SolderedElectronics/Soldered-Air-Quality-Device/Images/3dCase1.jpg

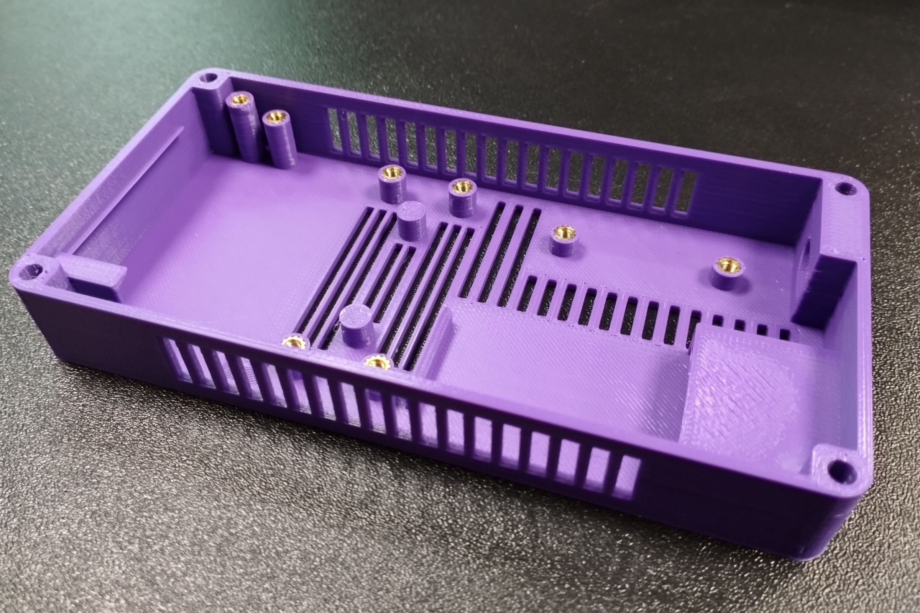
Images/3dCase1.jpg
