SolderedElectronics/Soldered-Air-Quality-Device/Images/3dCase.jpg

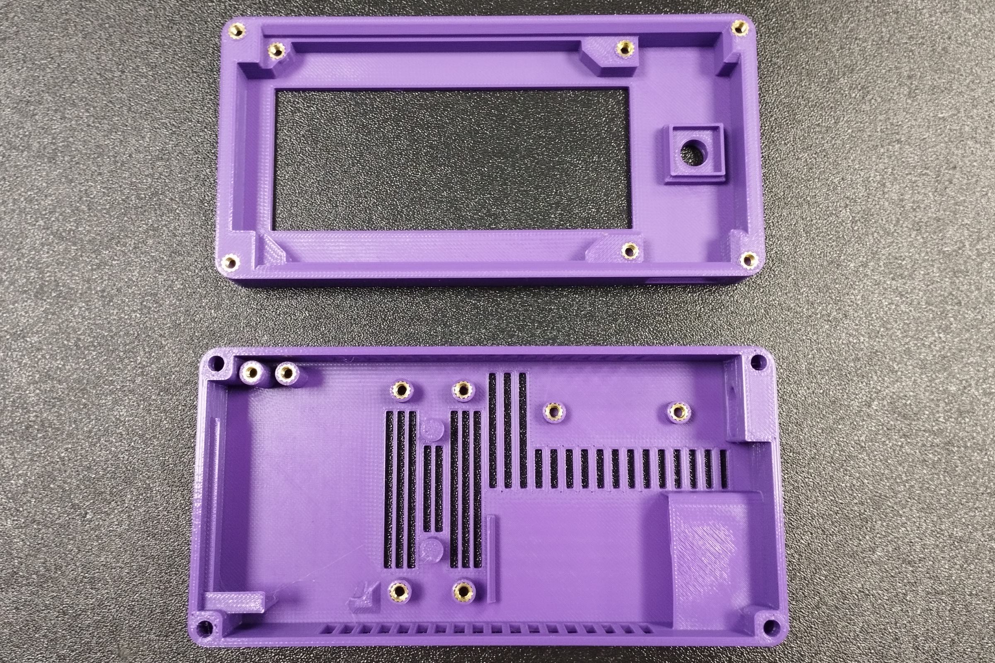
Images/3dCase.jpg
