SolderedElectronics/Soldered-Air-Quality-Device/Images/DeviceFromAbove.jpg

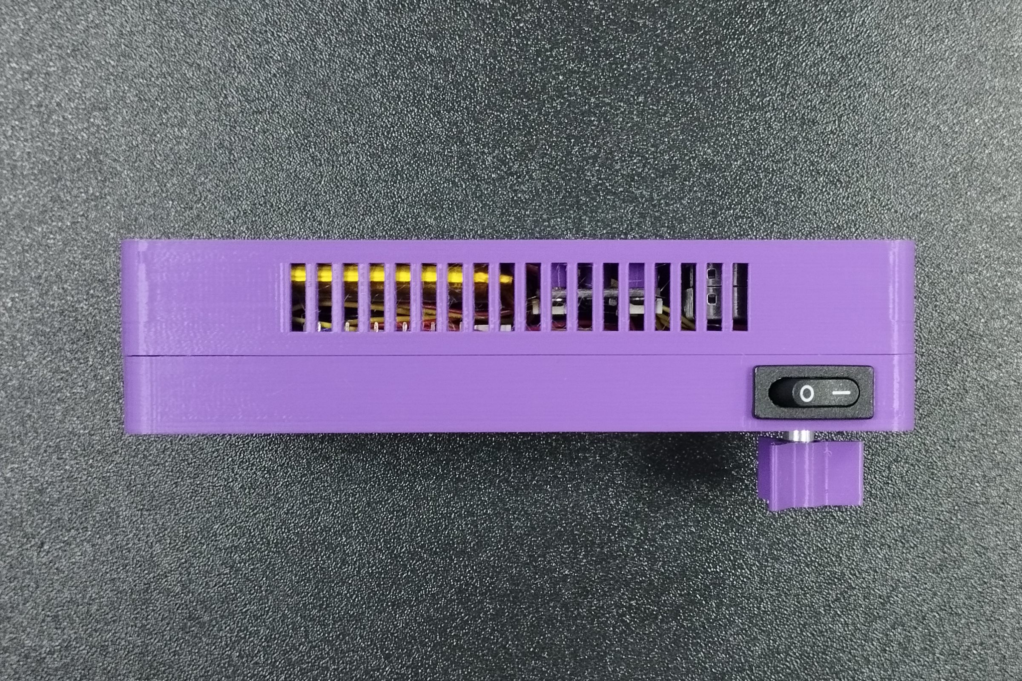
Images/DeviceFromAbove.jpg
