SolderedElectronics/Soldered-Air-Quality-Device/Images/knob for the rotary encoder.jpg

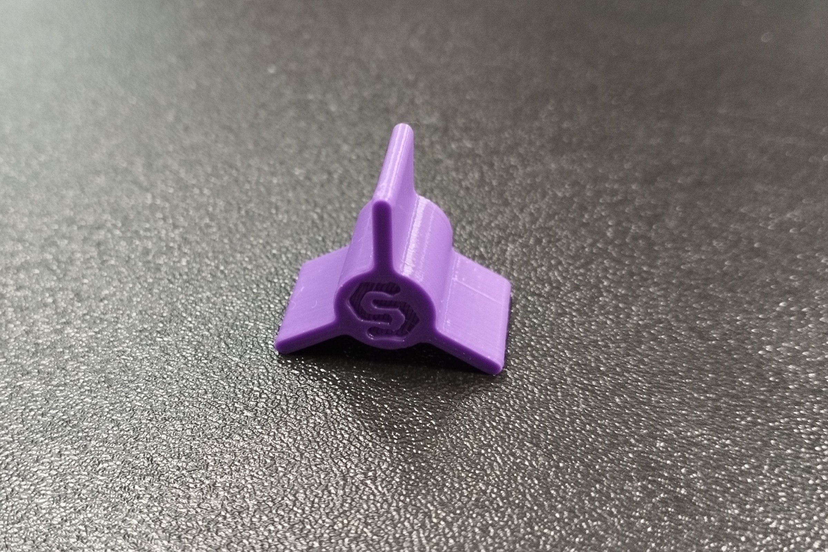
Images/knob for the rotary encoder.jpg
