SolderedElectronics/Soldered-Air-Quality-Device/Images/Page1.jpg

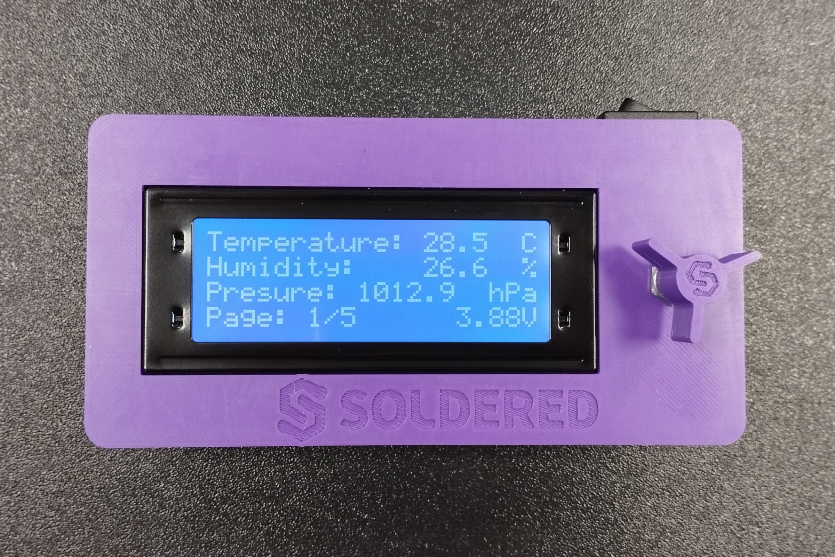
Images/Page1.jpg
