SolderedElectronics/Soldered-Air-Quality-Device/Images/Page3.jpg

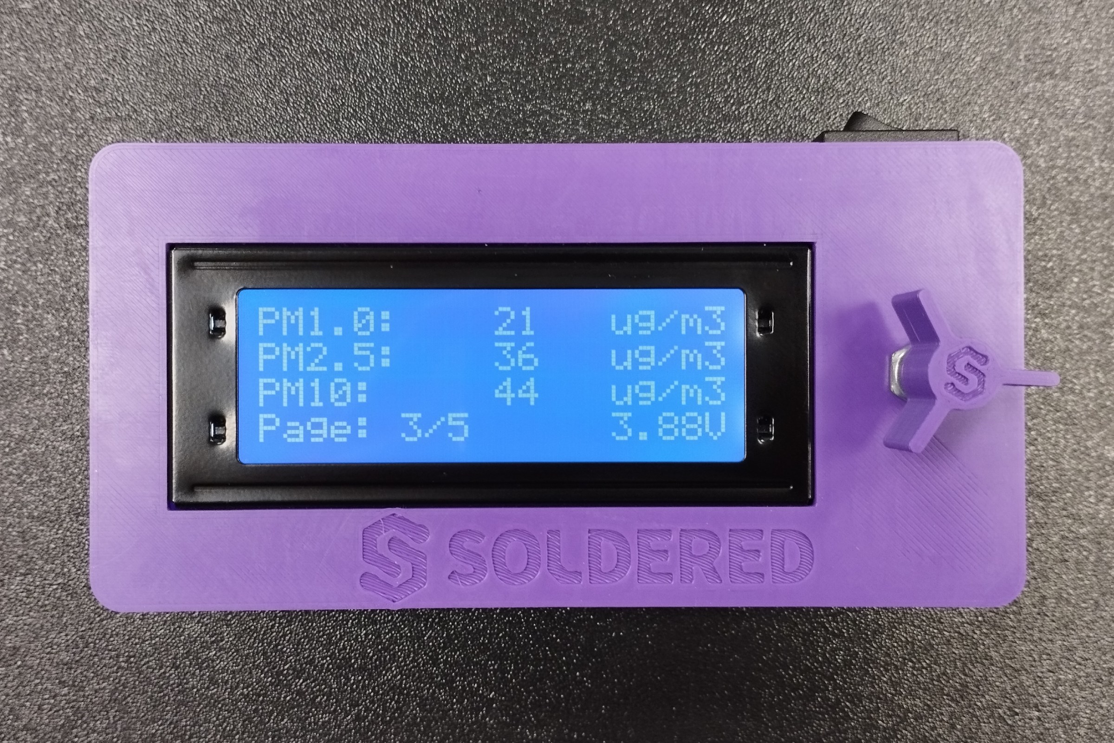
Images/Page3.jpg
